billieblaze/BBlazeSEQ/constants.h

// MIDI notes
#define  C   0
#define  Cs  1
#define  D   2
#define  Ds  3
#define  E   4
#define  F   5
#define  Fs  6
#define  G   7
#define  Gs  8
#define  A   9
#define  As  10
#define  B   11

// Octaves
#define  oct0  0
#define  oct1  12
#define  oct2  24
#define  oct3  36
#define  oct4  48
#define  oct5  60
#define  oct6  72
#define  oct7  84
